SystemsCyber/TruckCapeProjects/hardware/Enclosure Patterns and Graphics/TruckCape Bottom with DSUB Rev 3.pdf

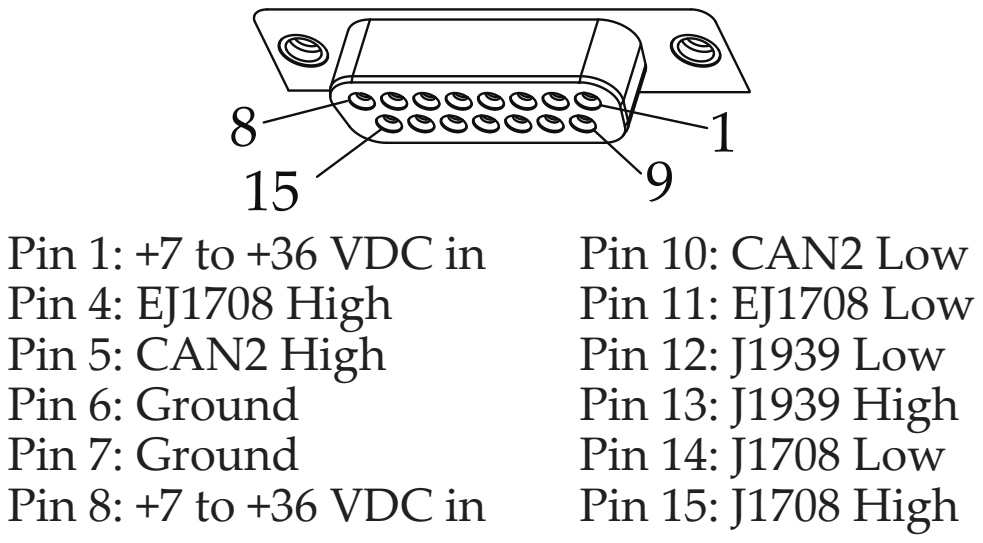
[picture p9: page 1]
Pin 10: CAN2 Low; Pin 12: J1939 Low Pin 13: J1939 High Pin 14: J1708 Low Pin 15: J1708 High; Pin 4: EJ1708 High; Pin 11: EJ1708 Low

Pin 1: +7 to +36 VDC in
Pin 5: CAN2 High
Pin 6: Ground
Pin 7: Ground
Pin 8: +7 to +36 VDC in
