SystemsCyber/TruckCapeProjects/hardware/TruckCape v2 Schematic.pdf

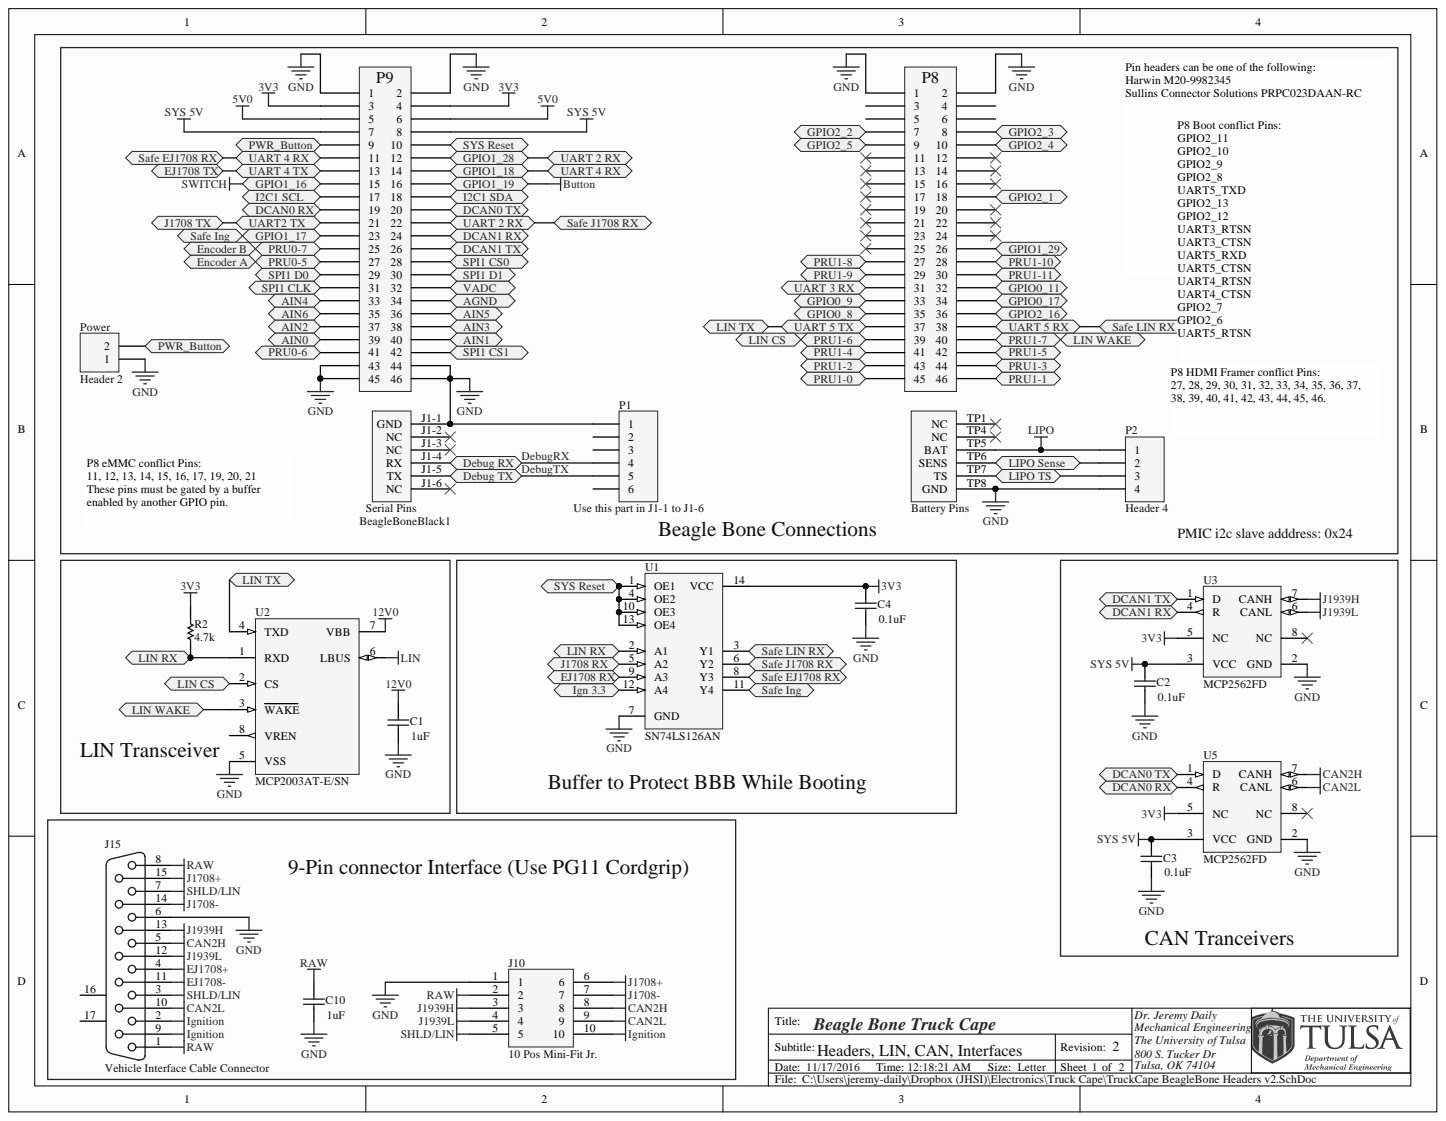
[picture p15: page 1]

Pin headers can be one of the following:
Harwin M20-9982345
Sullins Connector Solutions PRPC023DAAN-RC

These pins must be gated by a buffer
enabled by another GPIO pin.

Use this part in J1-1 to J1-6

Buffer to Protect BBB While Booting

9-Pin connector Interface (Use PG11 Cordgrip)

Title:
Beagle Bone Truck Cape

Dr. Jeremy Daily
Mechanical Engineering
The University of Tulsa
800 S. Tucker Dr
Tulsa, OK 74104

Headers, LIN, CAN, Interfaces Subtitle: | 2 Revision:

10 Pos Mini-Fit Jr.

Date: 11/17/2016 Time: 12:18:21 AM Size: Letter | Sheet 1 of 2

Vehicle Interface Cable Connector

C:\Users\jeremy-daily\Dropbox (JHSI)\Electronics\Truck Cape\TruckCape BeagleBone Headers v2.SchDoc

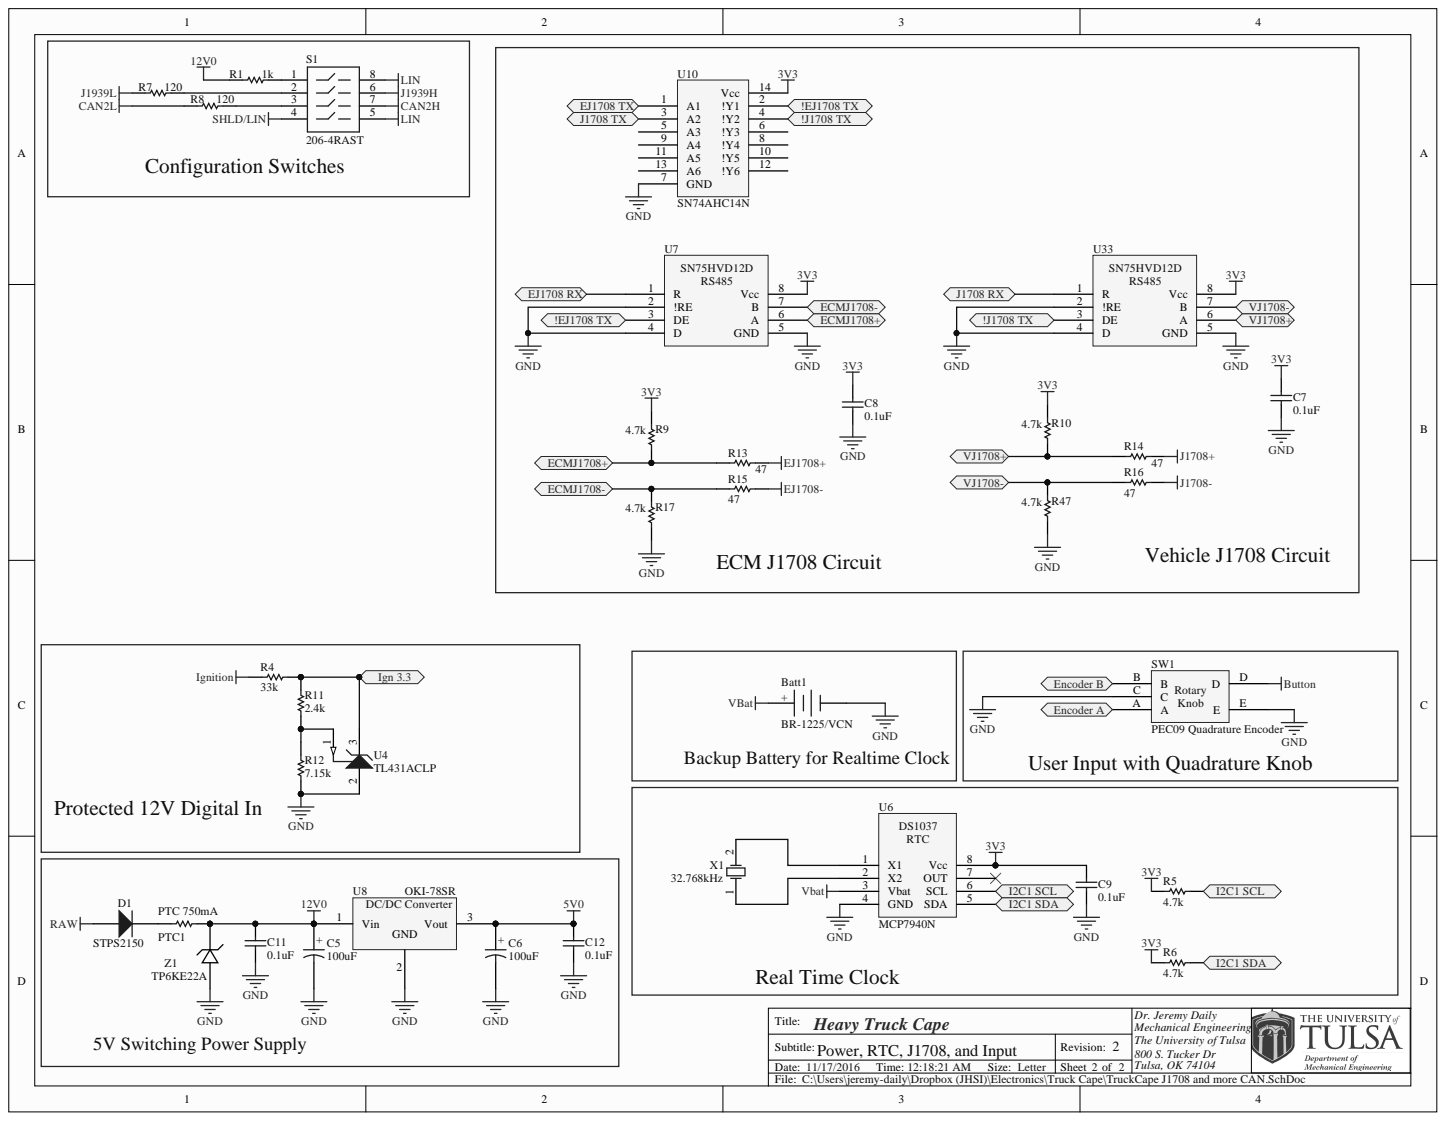
[picture p16: page 2]

R4 Protected 12V Digital In

Batt1 BR-1225/VCN Backup Battery for Realtime Clock | SW1

User Input with Quadrature Knob

Dr. Jeremy Daily
Mechanical Engineering
The University of Tulsa
800 S. Tucker Dr
Tulsa, OK 74104

Power, RTC, J1708, and Input Subtitle: | 2 Revision:

Date: 11/17/2016 Time: 12:18:21 AM Size: Letter | Sheet 2 of 2

C:\Users\jeremy-daily\Dropbox (JHSI)\Electronics\Truck Cape\TruckCape J1708 and more CAN.SchDoc

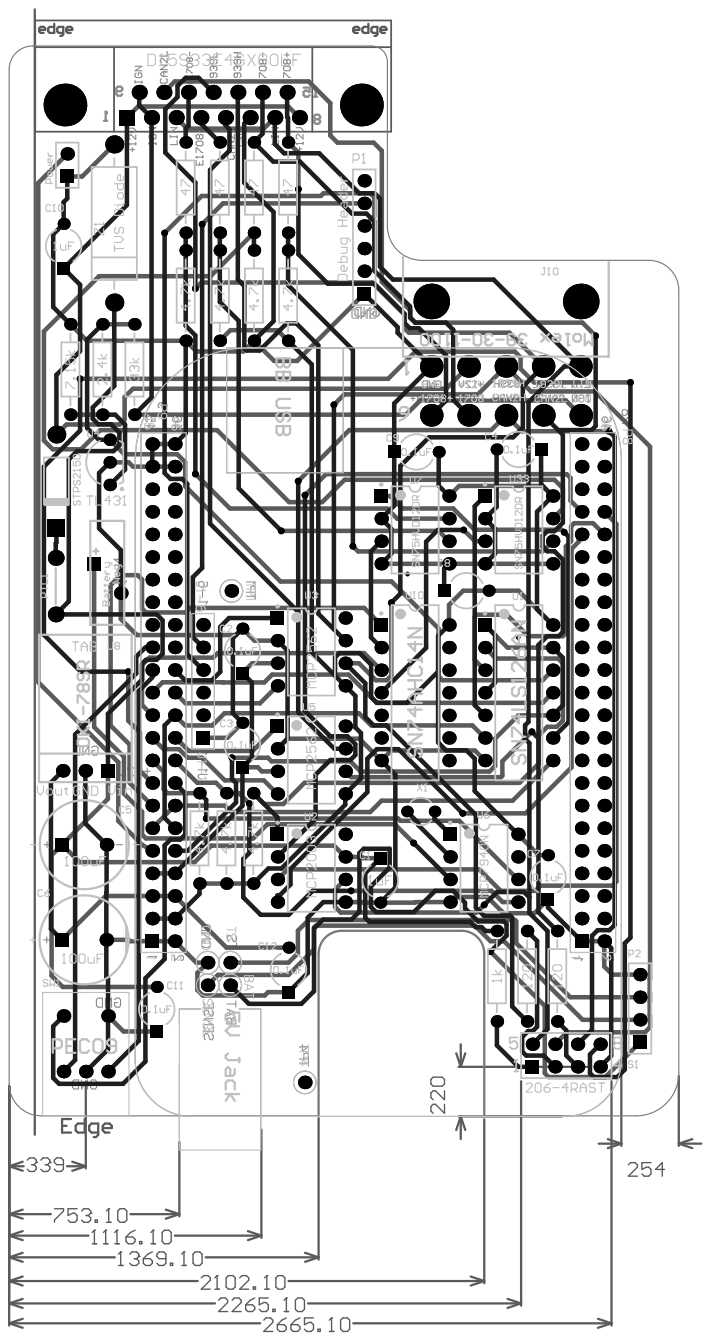
[picture p17: page 3]

# Board S
